paperlesspaper/paperlesspaper-hardware/paper7/pcb/EPAPER73_V2_pcb.jpg

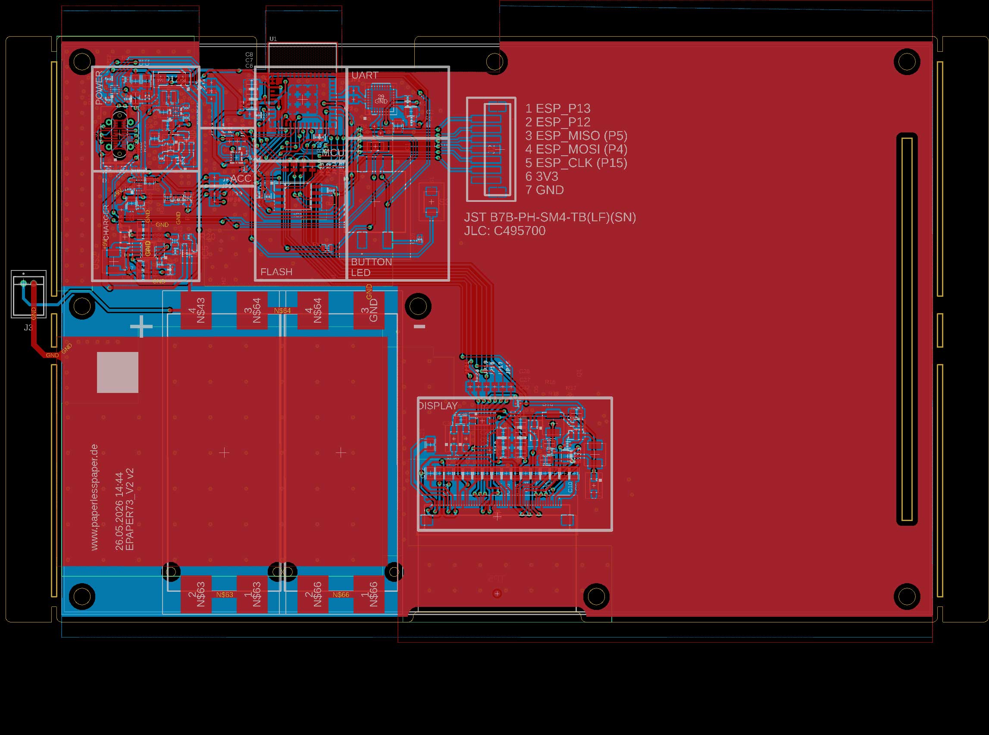
paper7/pcb/EPAPER73_V2_pcb.jpg
