paperlesspaper/paperlesspaper-hardware/paper7/pcb/EPAPER73_V2_sch.jpg

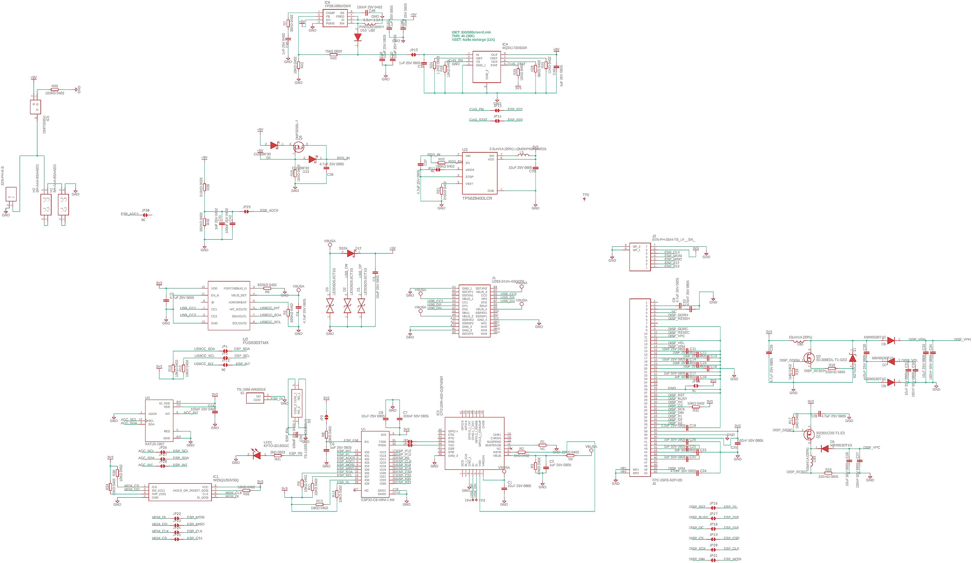
paper7/pcb/EPAPER73_V2_sch.jpg
